gearhead765/Van-Level/Notes/angleExample.png

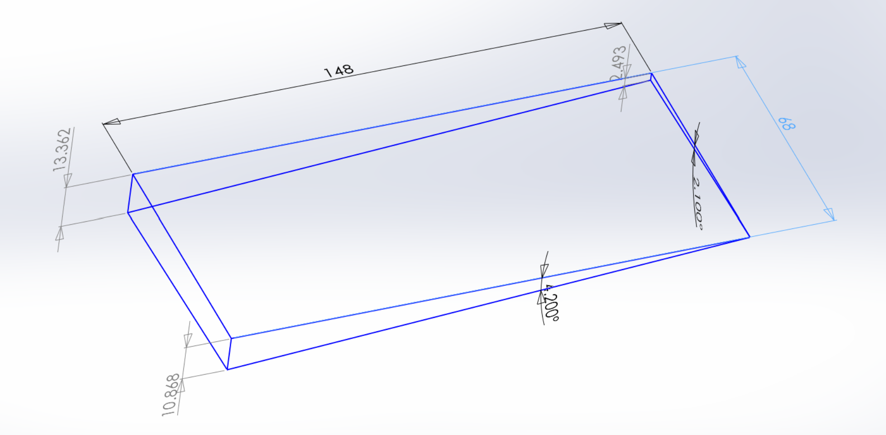
Notes/angleExample.png
