gearhead765/Van-Level/Notes/Phoenix sctew terminal blocks.png

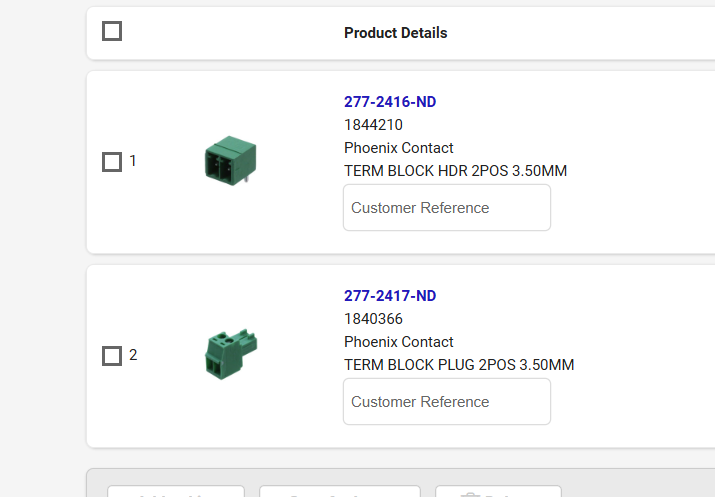
Notes/Phoenix sctew terminal blocks.png
