gearhead765/Van-Level/Van_Level_App/Van_Level/data/images/transit_top_transparent.png

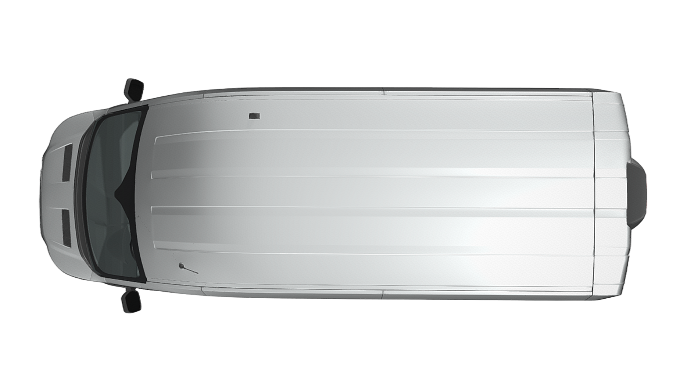
Van_Level_App/Van_Level/data/images/transit_top_transparent.png
